alicjamusial/LNA/images/filter.png

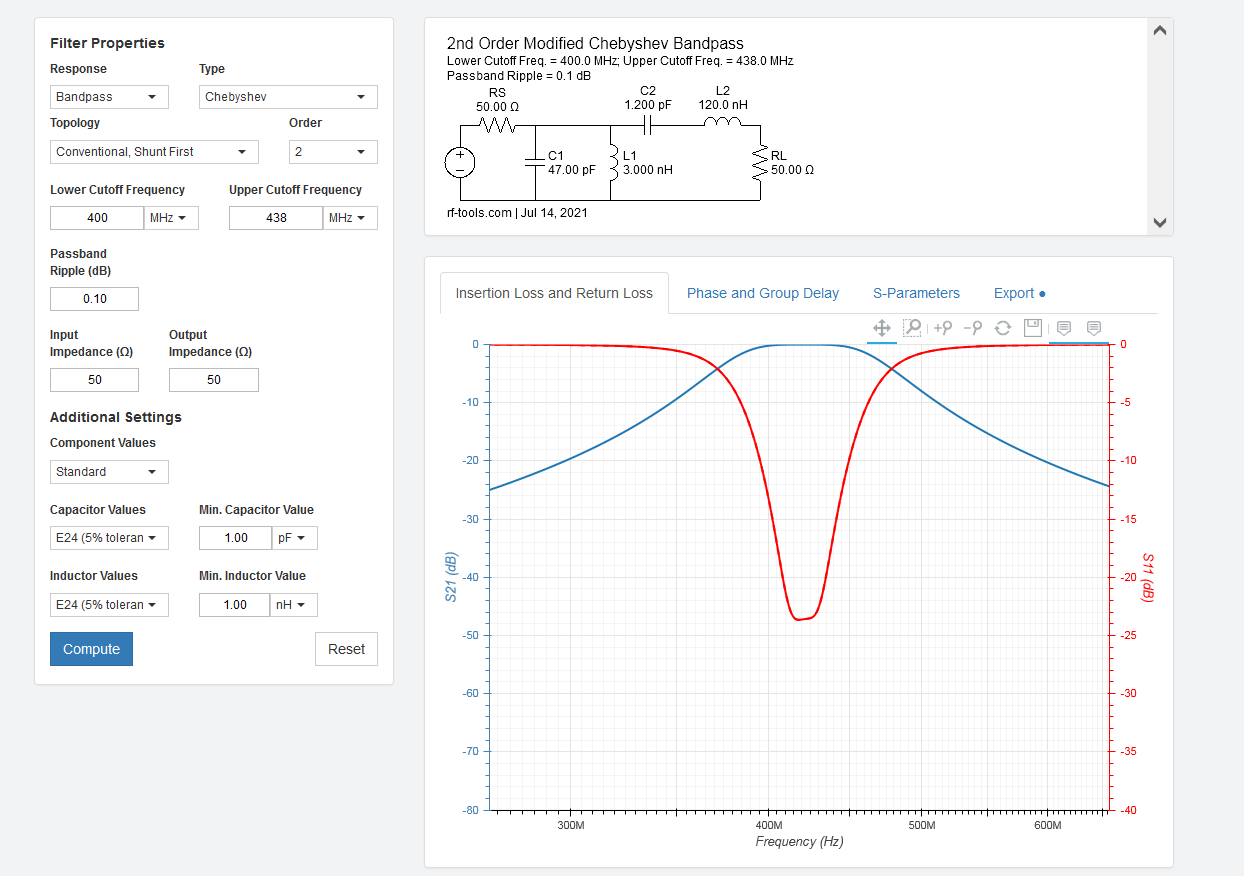
images/filter.png
