alicjamusial/LNA/images/imgs/2.png

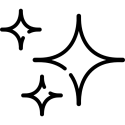
images/imgs/2.png
